Aahan-1105/simply-smart-wearable/Firmware/src/storage.h

#ifndef STORAGE_H
#define STORAGE_H

#include <Adafruit_LittleFS.h>
#include <InternalFileSystem.h>

using namespace Adafruit_LittleFS_Namespace;

class StorageManager {
public:
    StorageManager();
    bool begin();
    uint32_t loadStepCount();
    void saveStepCount(uint32_t steps);
};

#endif
